Gabriel220702/Robot-SCARA/SCARA Diseño/Final Assembly.SLDASM

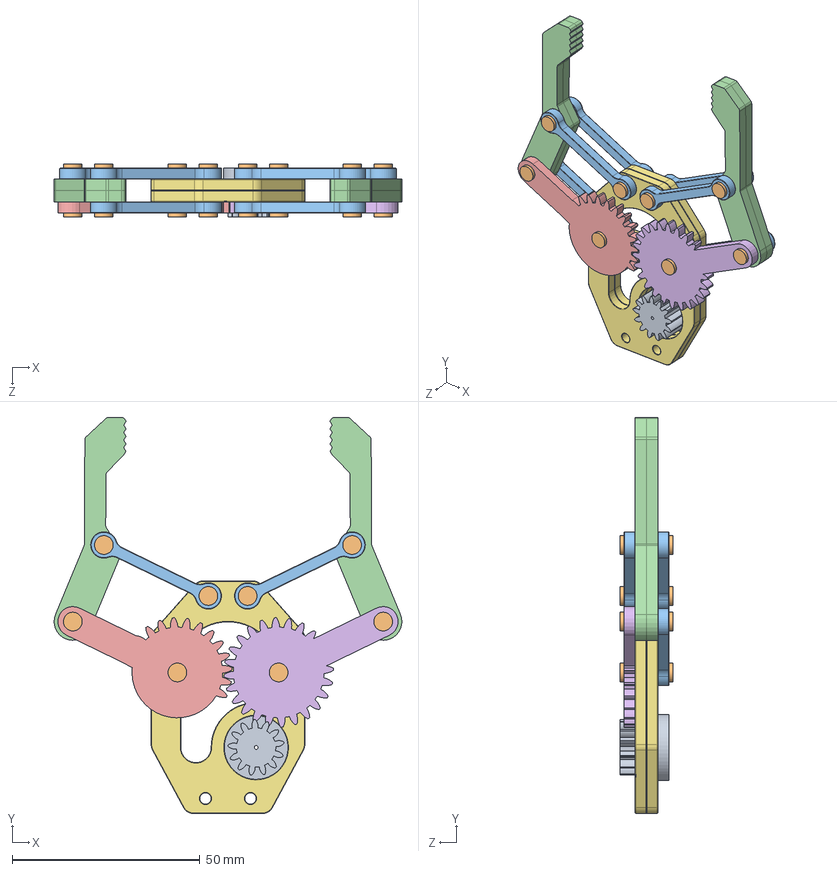
[picture p51: CAD file, 2025-12-15]
SCARA Diseño/Final Assembly.SLDASM
92.7 x 105.6 x 14.0 mm
Gear 1
Gear 2
Gripper x 4
Linkage x 6
Pin x 8
Motor Gear
