Gabriel220702/Robot-SCARA/SCARA Diseño/Base.SLDPRT

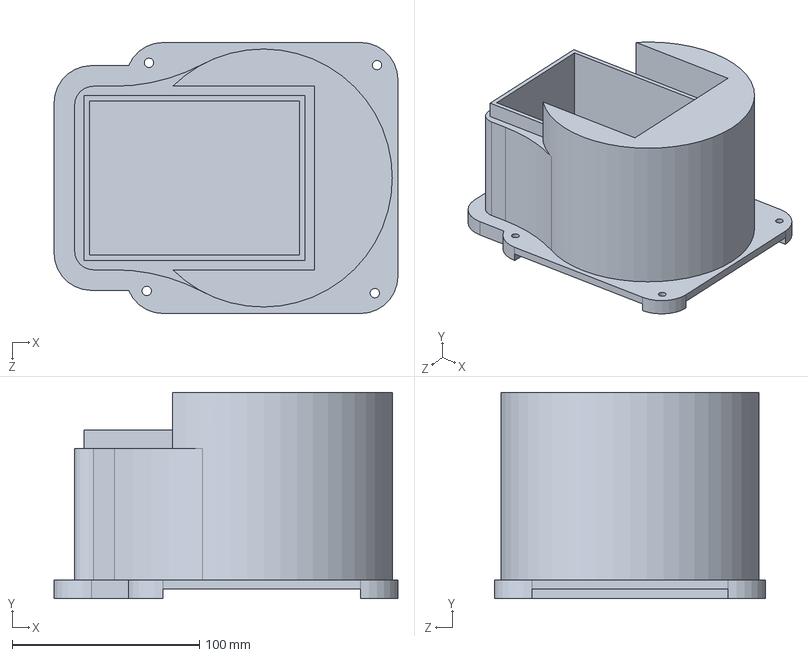
[picture p66: CAD file, 2025-12-15]
SCARA Diseño/Base.SLDPRT
183.6 x 110.0 x 144.7 mm
