Gabriel220702/Robot-SCARA/SCARA Diseño/Soporte del actuador lineal.SLDPRT

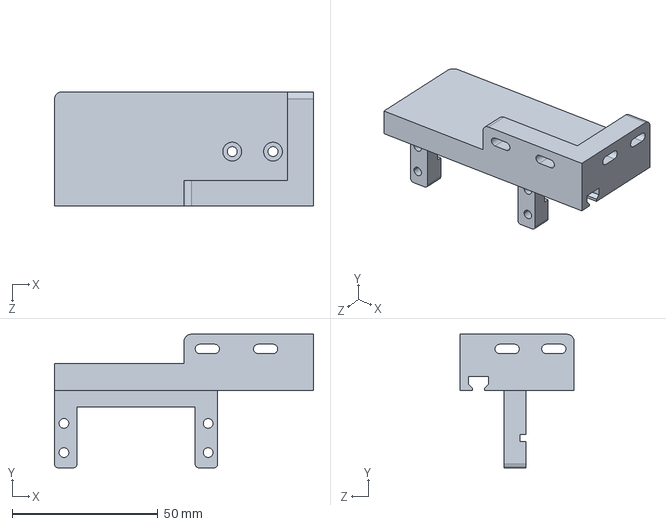
[picture p67: CAD file, 2025-12-15]
SCARA Diseño/Soporte del actuador lineal.SLDPRT
88.9 x 45.9 x 39.2 mm
