Gabriel220702/Robot-SCARA/SCARA Diseño/Tapa Eslabon 2.SLDPRT

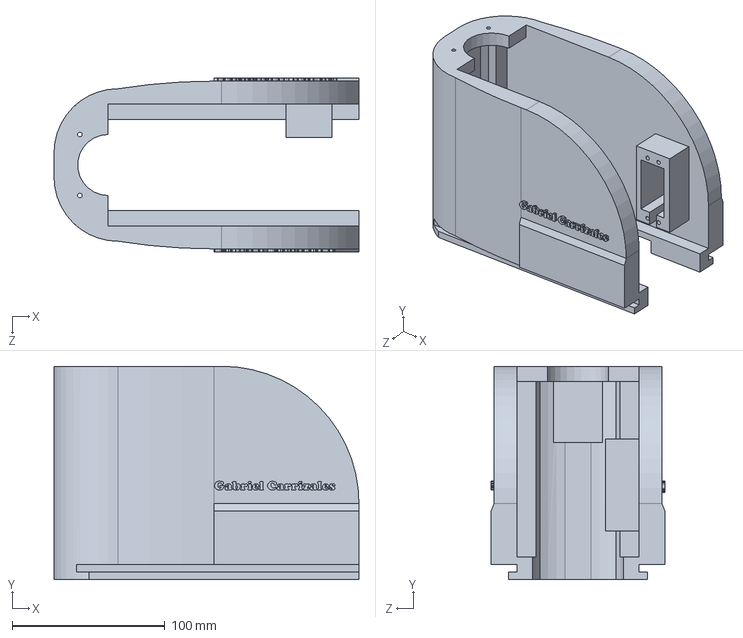
[picture p68: CAD file, 2025-12-15]
SCARA Diseño/Tapa Eslabon 2.SLDPRT
200.0 x 140.0 x 114.0 mm
