Gabriel220702/Robot-SCARA/SCARA Diseño/Tapita.SLDPRT

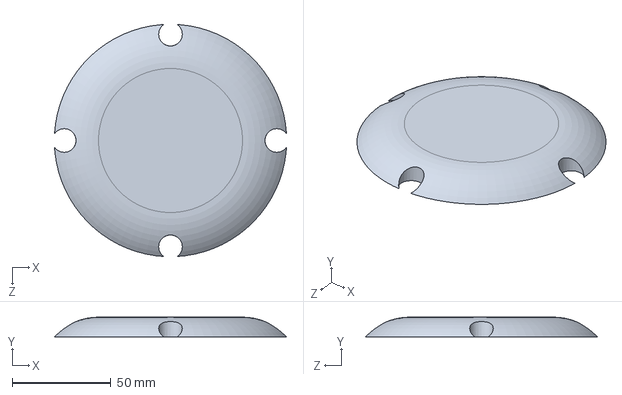
[picture p69: CAD file, 2025-12-15]
SCARA Diseño/Tapita.SLDPRT
117.4 x 10.0 x 117.4 mm
