Gabriel220702/Robot-SCARA/SCARA Diseño/extension.SLDPRT

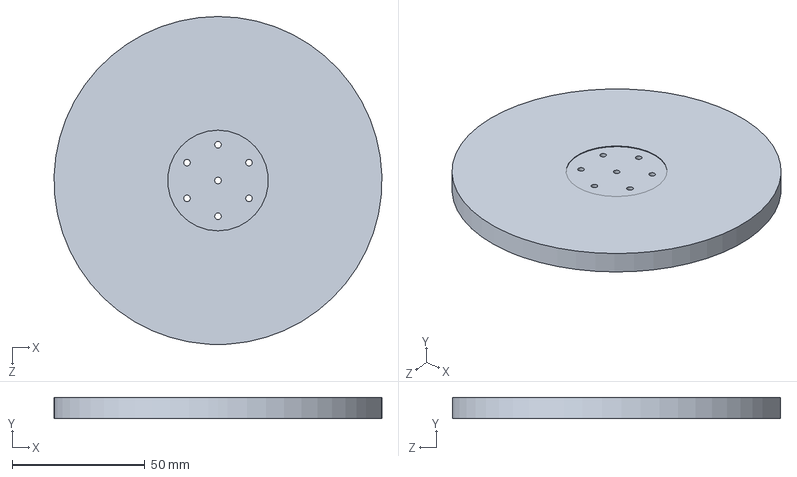
[picture p70: CAD file, 2025-12-15]
SCARA Diseño/extension.SLDPRT
123.7 x 8.00 x 123.8 mm
