Gabriel220702/Robot-SCARA/SCARA Diseño/Eslabón 1.SLDPRT

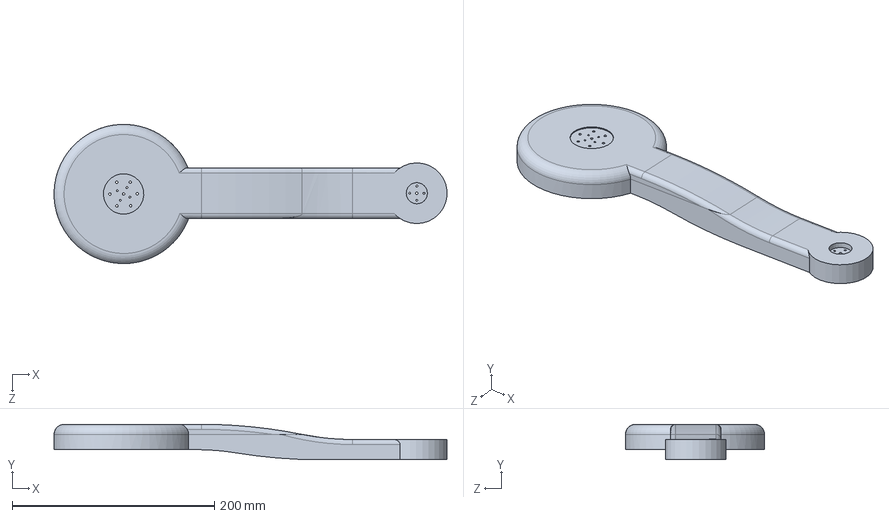
[picture p71: CAD file, 2025-12-15]
SCARA Diseño/Eslabón 1.SLDPRT
388.5 x 35.0 x 137.5 mm
