Gabriel220702/Robot-SCARA/SCARA Diseño/Enchufe.SLDPRT

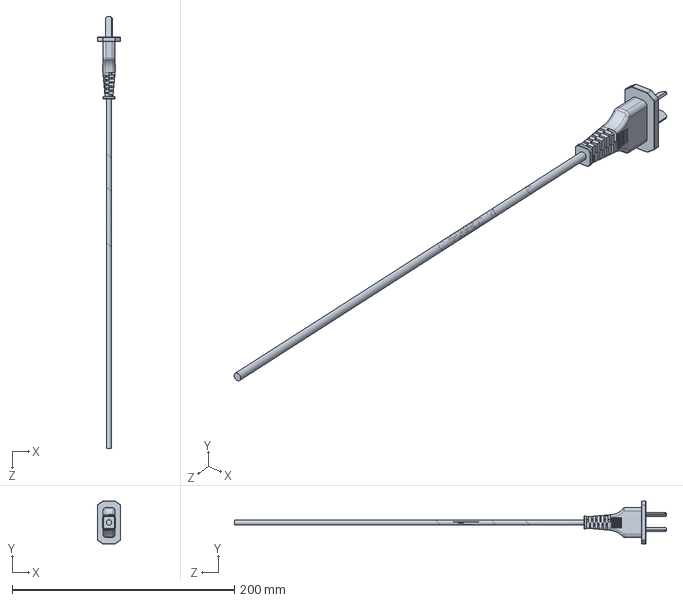
[picture p72: CAD file, 2025-12-15]
SCARA Diseño/Enchufe.SLDPRT
21.0 x 38.6 x 388.5 mm
