Gabriel220702/Robot-SCARA/SCARA Diseño/Tapa Base.SLDPRT

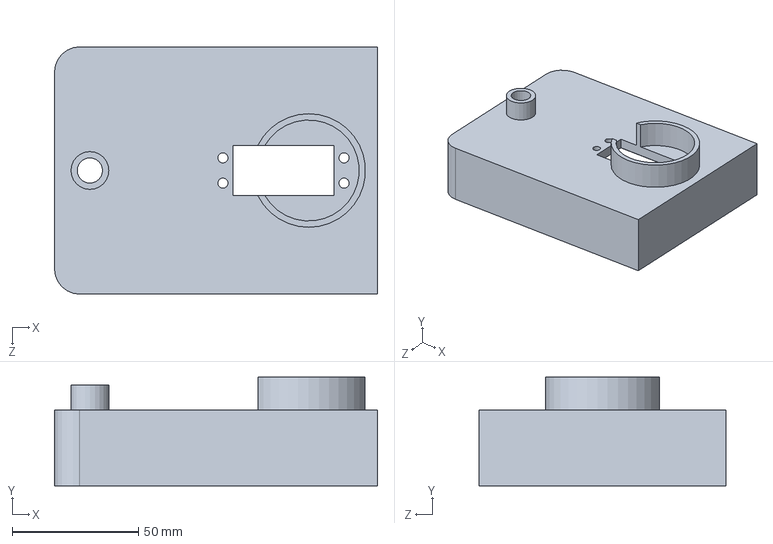
[picture p73: CAD file, 2025-12-15]
SCARA Diseño/Tapa Base.SLDPRT
128.0 x 43.0 x 98.0 mm
