Gabriel220702/Robot-SCARA/SCARA Diseño/Tapa final.SLDPRT

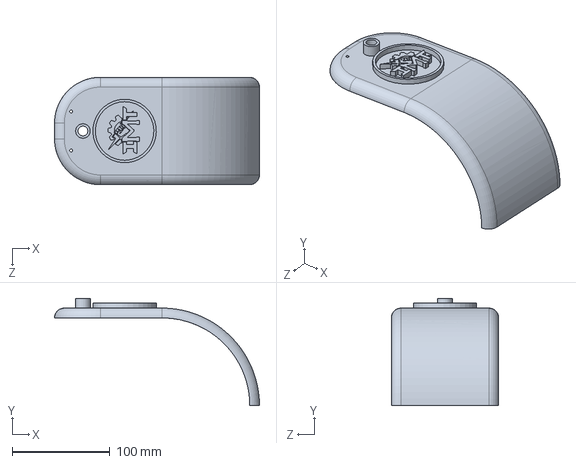
[picture p74: CAD file, 2025-12-15]
SCARA Diseño/Tapa final.SLDPRT
210.0 x 110.0 x 110.0 mm
