Gabriel220702/Robot-SCARA/SCARA Diseño/Eslabon 2.SLDPRT

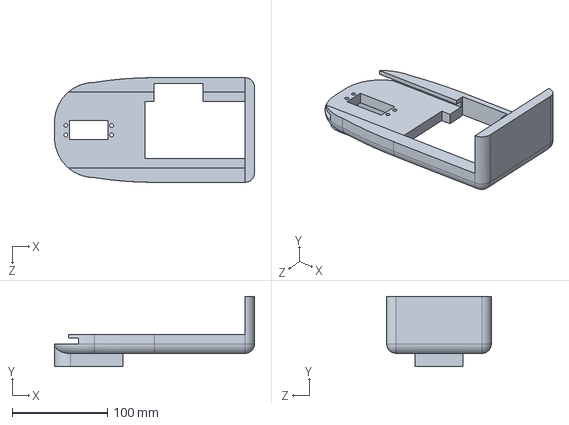
[picture p75: CAD file, 2025-12-15]
SCARA Diseño/Eslabon 2.SLDPRT
210.0 x 74.0 x 110.0 mm
