Gabriel220702/Robot-SCARA/SCARA Diseño/Part4.SLDPRT

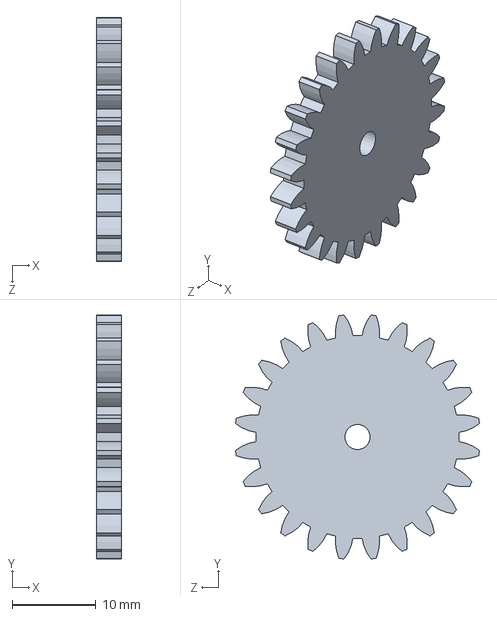
[picture p76: CAD file, 2025-12-15]
SCARA Diseño/Part4.SLDPRT
3.00 x 29.1 x 29.1 mm
