Gabriel220702/Robot-SCARA/SCARA Diseño/Gripper.SLDPRT

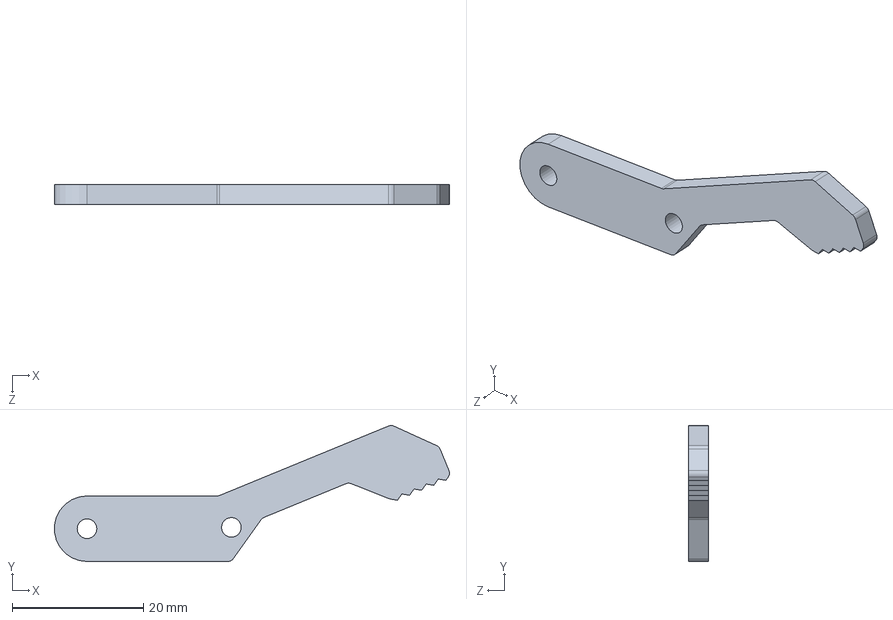
[picture p77: CAD file, 2025-12-15]
SCARA Diseño/Gripper.SLDPRT
60.3 x 20.7 x 3.00 mm
