Gabriel220702/Robot-SCARA/SCARA Diseño/Gear 1.SLDPRT

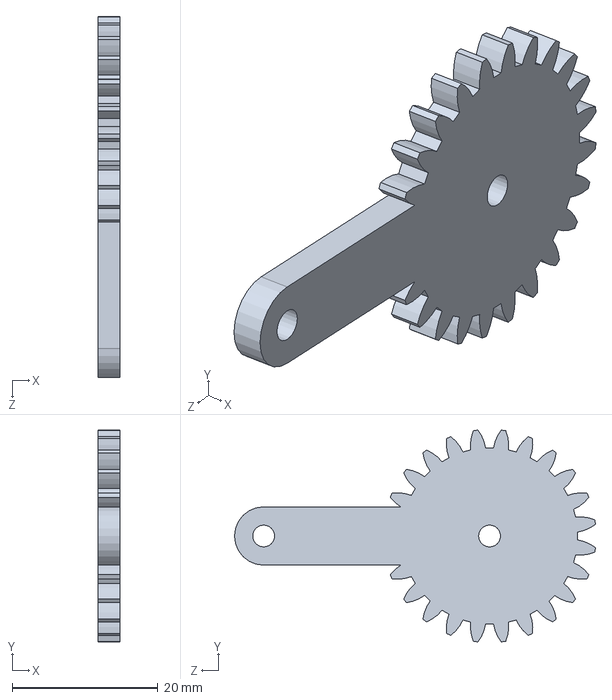
[picture p78: CAD file, 2025-12-15]
SCARA Diseño/Gear 1.SLDPRT
3.00 x 29.1 x 49.5 mm
