Gabriel220702/Robot-SCARA/SCARA Diseño/Gear 2.SLDPRT

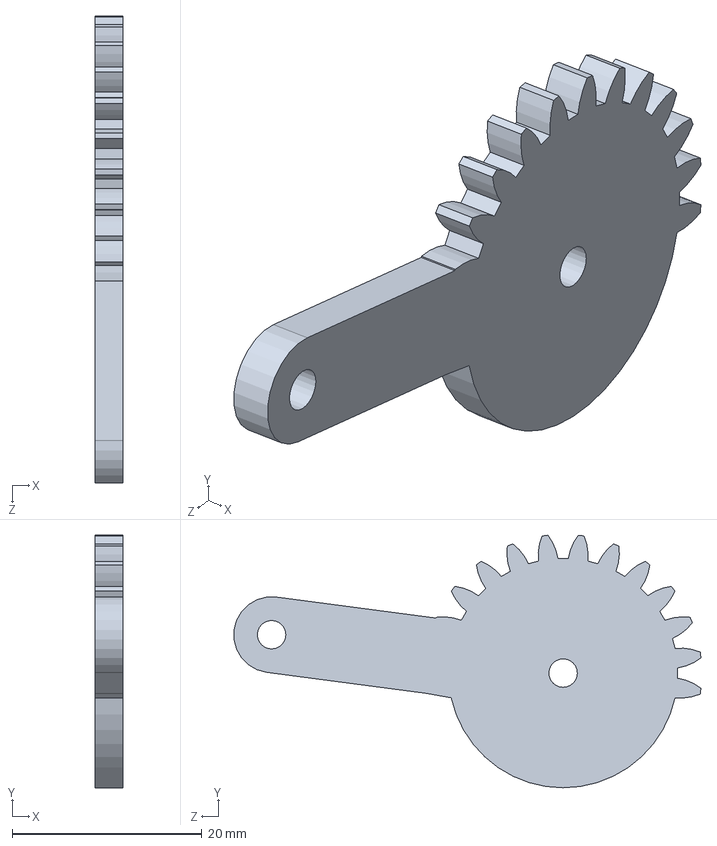
[picture p79: CAD file, 2025-12-15]
SCARA Diseño/Gear 2.SLDPRT
3.00 x 26.6 x 49.2 mm
