Gabriel220702/Robot-SCARA/SCARA Diseño/Body.SLDPRT

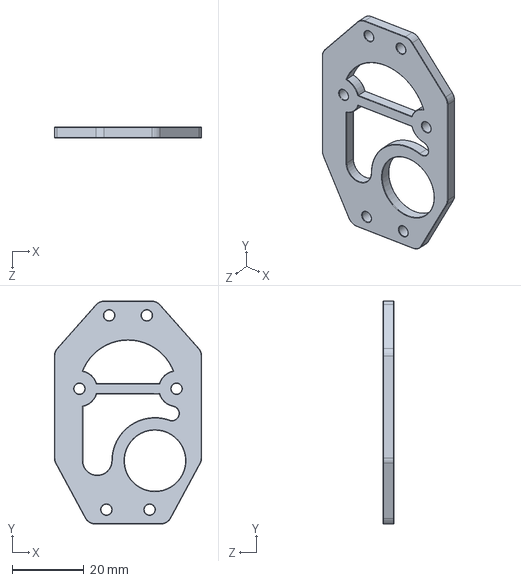
[picture p80: CAD file, 2025-12-15]
SCARA Diseño/Body.SLDPRT
41.0 x 62.0 x 3.00 mm
