Gabriel220702/Robot-SCARA/SCARA Diseño/Linkage.SLDPRT

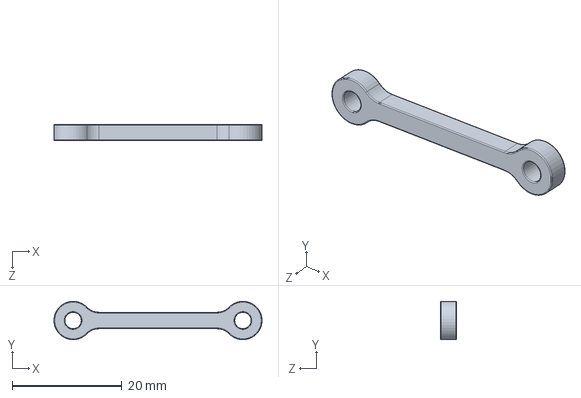
[picture p81: CAD file, 2025-12-15]
SCARA Diseño/Linkage.SLDPRT
38.0 x 7.00 x 3.00 mm
