Gabriel220702/Robot-SCARA/SCARA Diseño/Motor Gear.SLDPRT

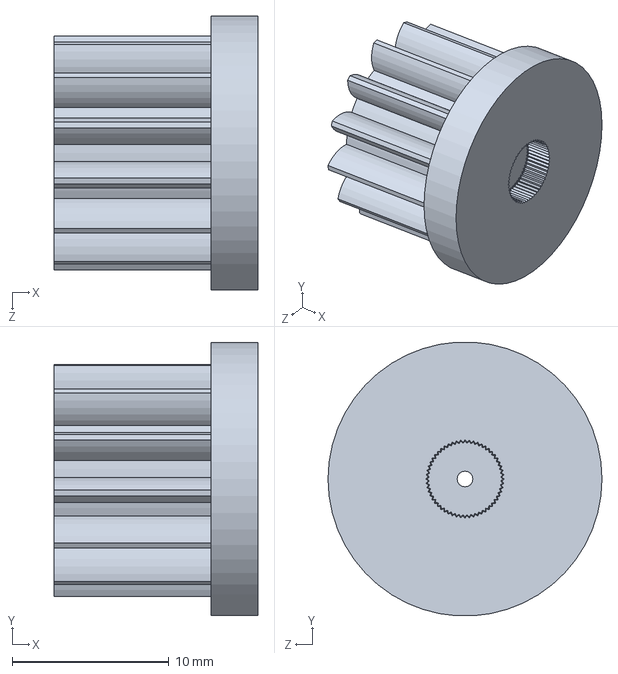
[picture p82: CAD file, 2025-12-15]
SCARA Diseño/Motor Gear.SLDPRT
13.0 x 17.5 x 17.5 mm
