Gabriel220702/Robot-SCARA/SCARA Diseño/Pin.SLDPRT

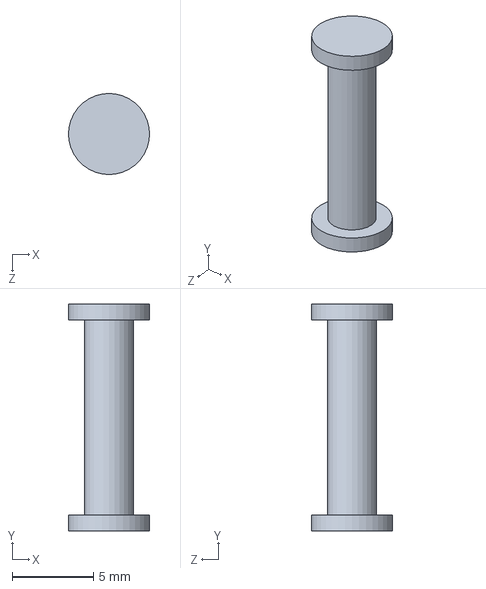
[picture p83: CAD file, 2025-12-15]
SCARA Diseño/Pin.SLDPRT
5.00 x 14.0 x 5.00 mm
