Gabriel220702/Robot-SCARA/SCARA Diseño/Part9 - Gear 4.SLDPRT

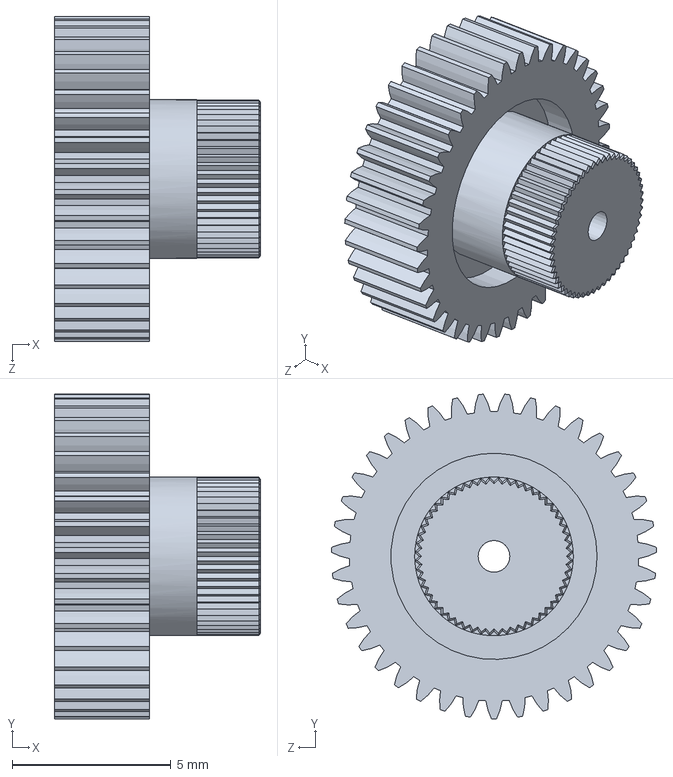
[picture p84: CAD file, 2025-12-15]
SCARA Diseño/Part9 - Gear 4.SLDPRT
6.50 x 10.2 x 10.2 mm
