Gabriel220702/Robot-SCARA/SCARA Diseño/Cubo 3.SLDPRT

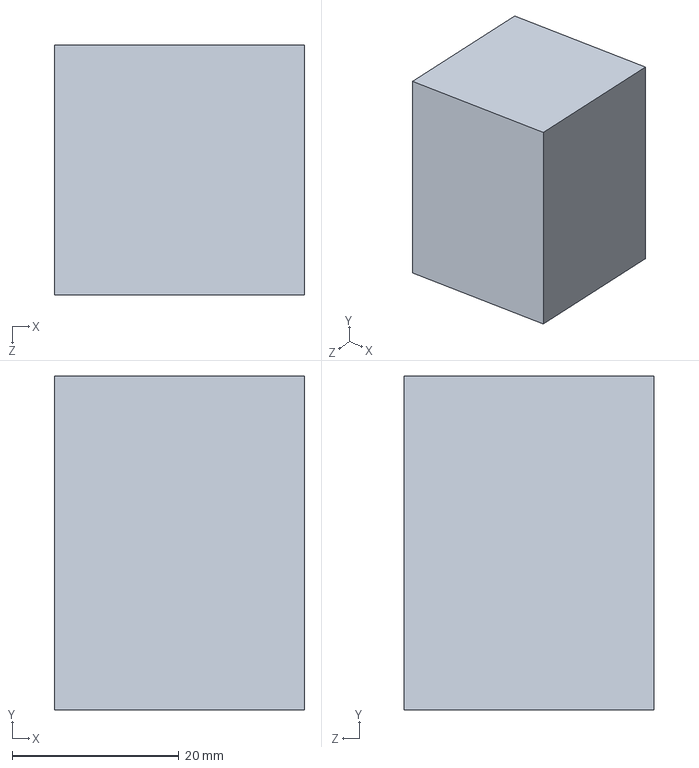
[picture p85: CAD file, 2025-12-15]
SCARA Diseño/Cubo 3.SLDPRT
30.0 x 40.0 x 30.0 mm
