Gabriel220702/Robot-SCARA/SCARA Diseño/Base 2.SLDPRT

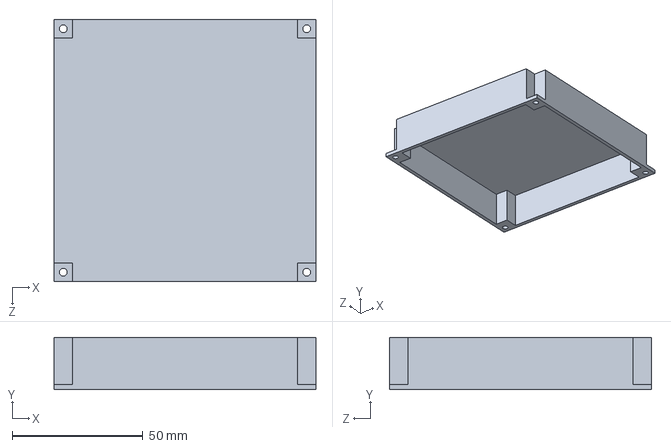
[picture p86: CAD file, 2025-12-15]
SCARA Diseño/Base 2.SLDPRT
100.0 x 20.0 x 100.0 mm
