Gabriel220702/Robot-SCARA/SCARA Diseño/Base 3.SLDPRT

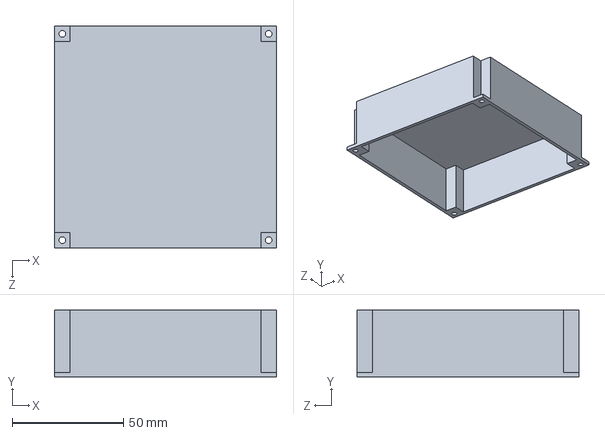
[picture p87: CAD file, 2025-12-15]
SCARA Diseño/Base 3.SLDPRT
100.0 x 30.0 x 100.0 mm
