Gabriel220702/Robot-SCARA/SCARA Diseño/Base pedorra.SLDPRT

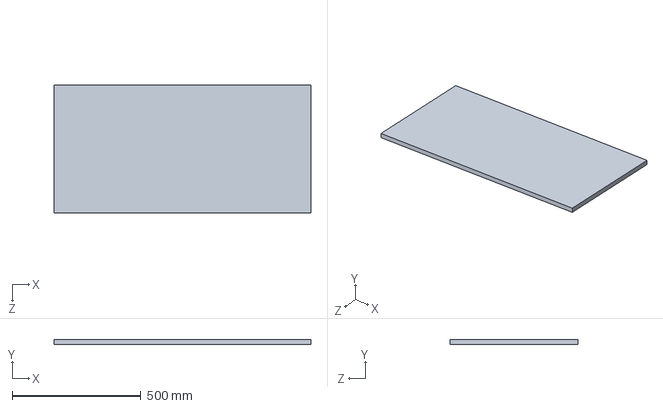
[picture p88: CAD file, 2025-12-15]
SCARA Diseño/Base pedorra.SLDPRT
1000.0 x 20.0 x 500.0 mm
