Gabriel220702/Robot-SCARA/SCARA Diseño/Base 4.SLDPRT

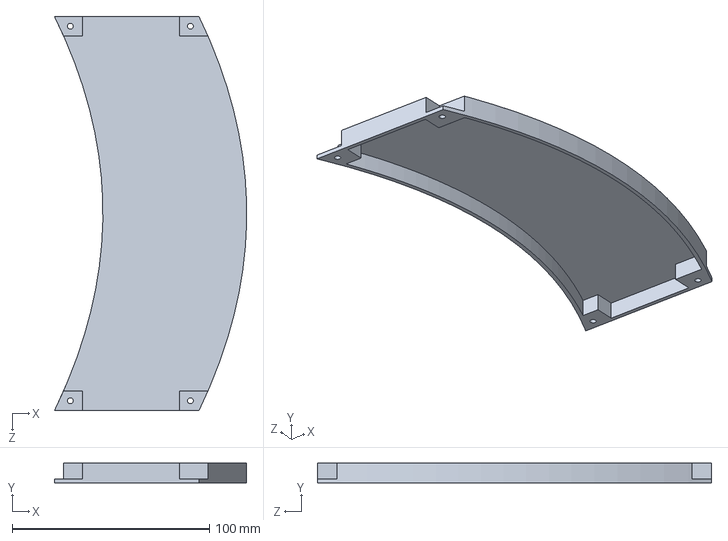
[picture p89: CAD file, 2025-12-15]
SCARA Diseño/Base 4.SLDPRT
97.6 x 10.0 x 200.0 mm
