Gabriel220702/Robot-SCARA/SCARA Diseño/Cubo 2.SLDPRT

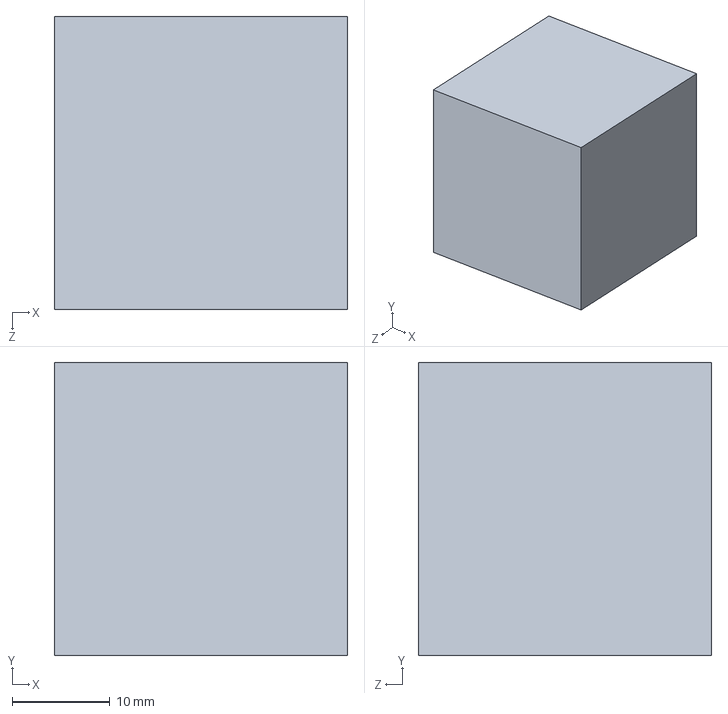
[picture p90: CAD file, 2025-12-15]
SCARA Diseño/Cubo 2.SLDPRT
30.0 x 30.0 x 30.0 mm
