Gabriel220702/Robot-SCARA/SCARA Diseño/Base 1.SLDPRT

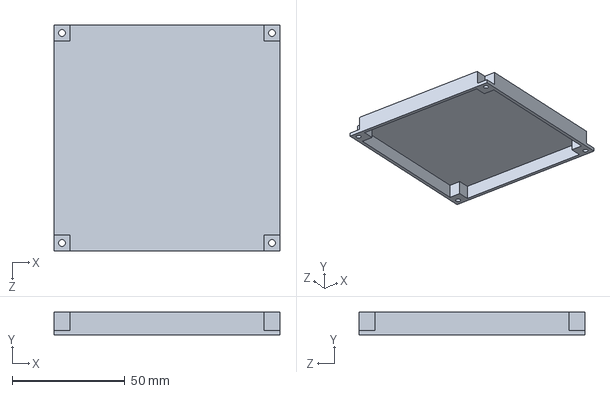
[picture p91: CAD file, 2025-12-15]
SCARA Diseño/Base 1.SLDPRT
100.0 x 10.0 x 100.0 mm
