Gabriel220702/Robot-SCARA/SCARA Diseño/Cubo 1.SLDPRT

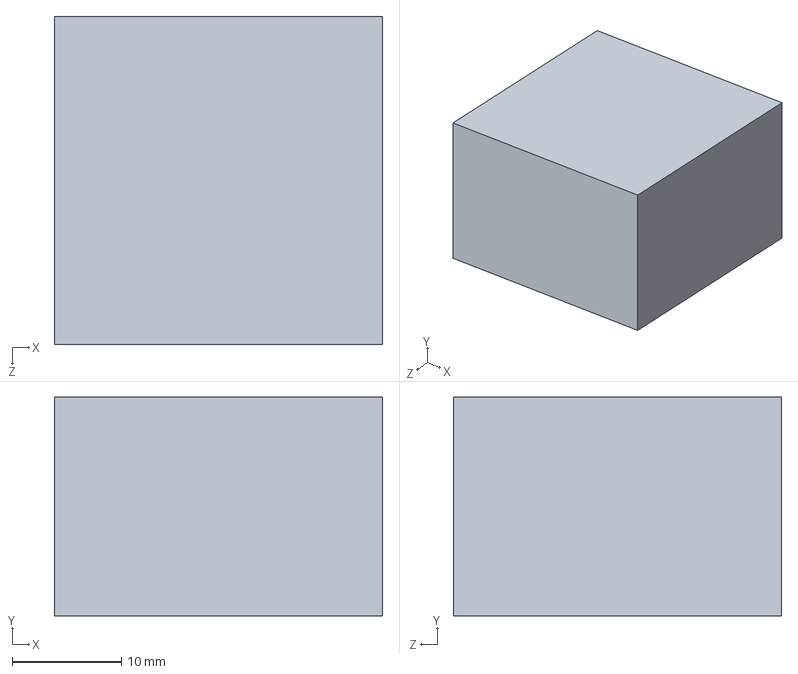
[picture p92: CAD file, 2025-12-15]
SCARA Diseño/Cubo 1.SLDPRT
30.0 x 20.0 x 30.0 mm
