Gabriel220702/Robot-SCARA/SCARA Diseño/Headers Hembra.SLDASM

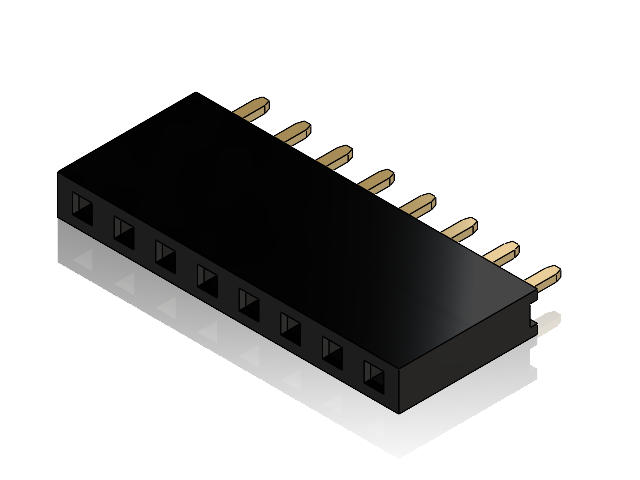
[picture p93: CAD file, 2025-12-15]
SCARA Diseño/Headers Hembra.SLDASM
Steckleiste.step
Stift.step
