Gabriel220702/Robot-SCARA/SCARA Diseño/ESP32-C3.SLDASM

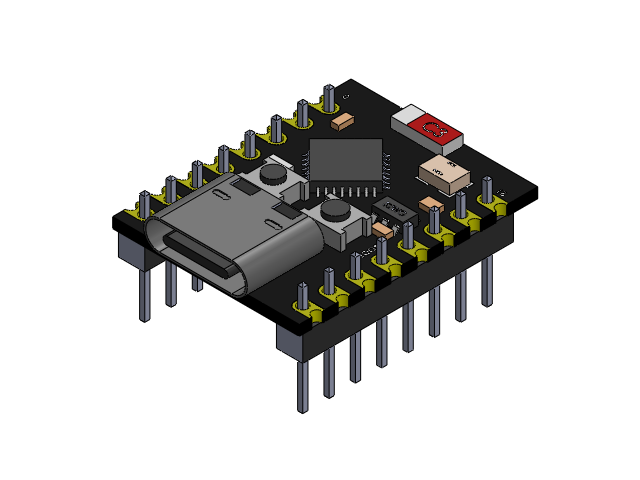
[picture p94: CAD file, 2025-12-15]
SCARA Diseño/ESP32-C3.SLDASM
ESP32 C3 Super mini.STEP
Male_PIN_X8.STEP x 2
