Gabriel220702/Robot-SCARA/SCARA Diseño/Headers Macho.SLDASM

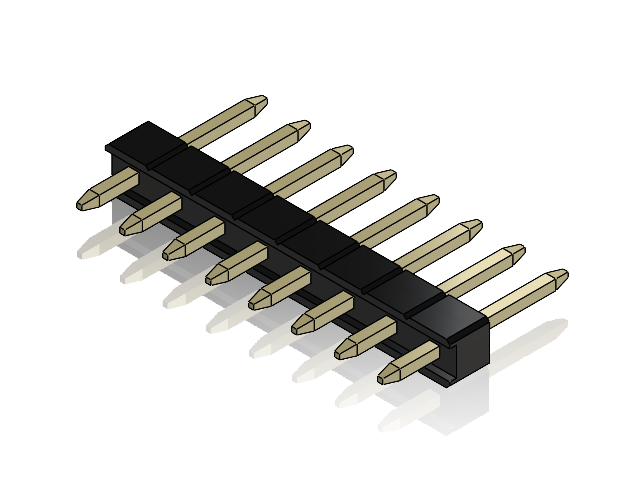
[picture p95: CAD file, 2025-12-15]
SCARA Diseño/Headers Macho.SLDASM
Stift_1.step
Klammer.step
